CICATA/covid19/Adulto.jpeg

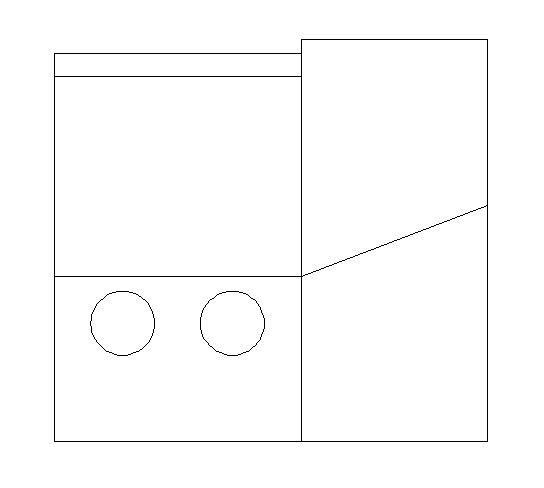
Adulto.jpeg
