CICATA/covid19/cronologia/IMG-20200330-WA0012.jpg

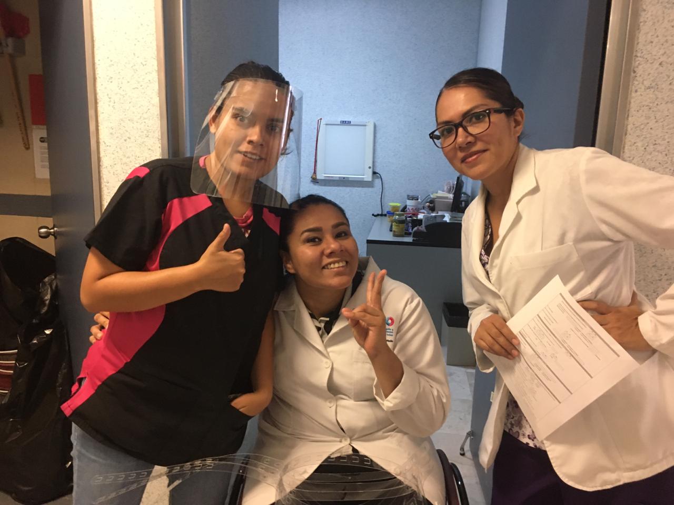
cronologia/IMG-20200330-WA0012.jpg
