CICATA/covid19/cronologia/IMG-20200331-WA0063.jpg

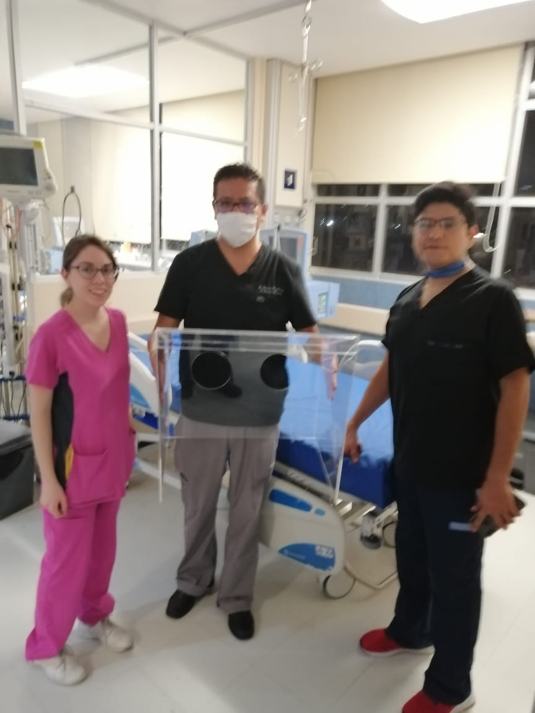
cronologia/IMG-20200331-WA0063.jpg
