CICATA/covid19/cronologia/IMG_20200404_121659562_HDR.jpg

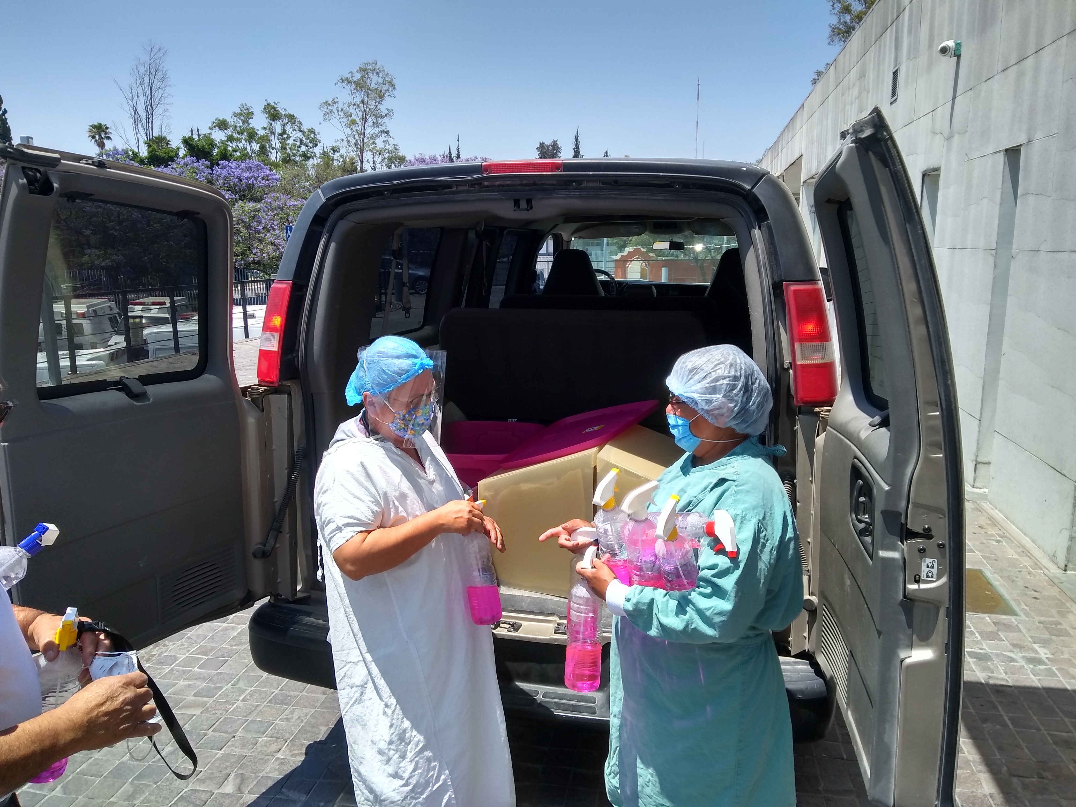
cronologia/IMG_20200404_121659562_HDR.jpg
