CICATA/covid19/Nino.jpeg

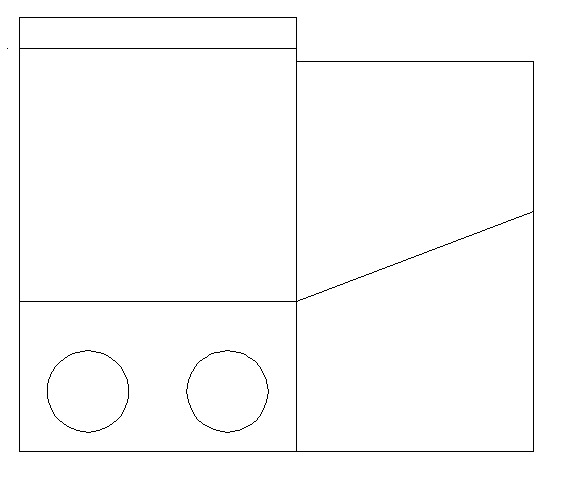
Nino.jpeg
